cpatagon/microSD_PCB/doc/img/huellas_pcb.png

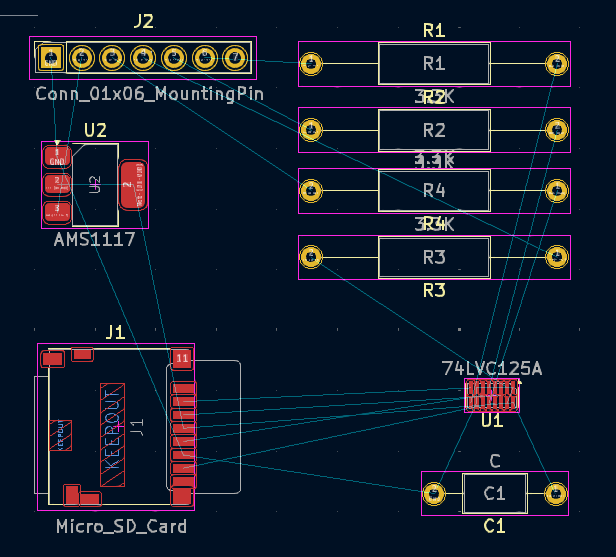
doc/img/huellas_pcb.png
