cpatagon/microSD_PCB/doc/propuesta/PlanoPCB.png

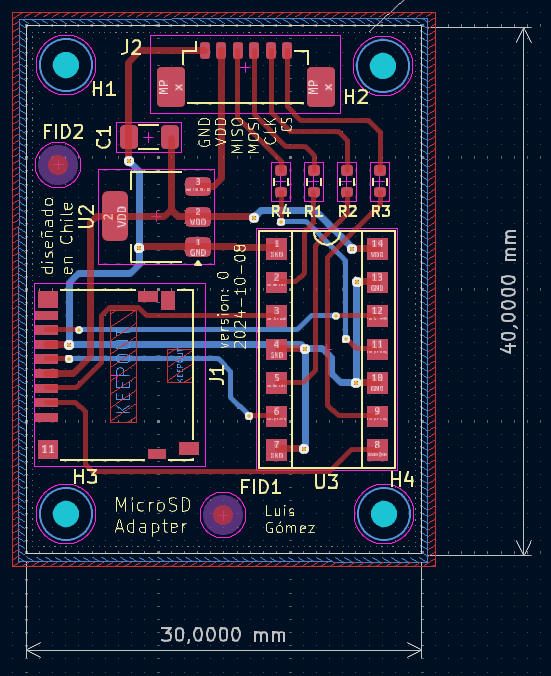
doc/propuesta/PlanoPCB.png
