cpatagon/microSD_PCB/info/img/package_superior_74LVC125A.png

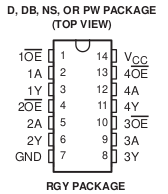
info/img/package_superior_74LVC125A.png
